qingwa2009/MyBLEGamepad/pcb/01.jpg

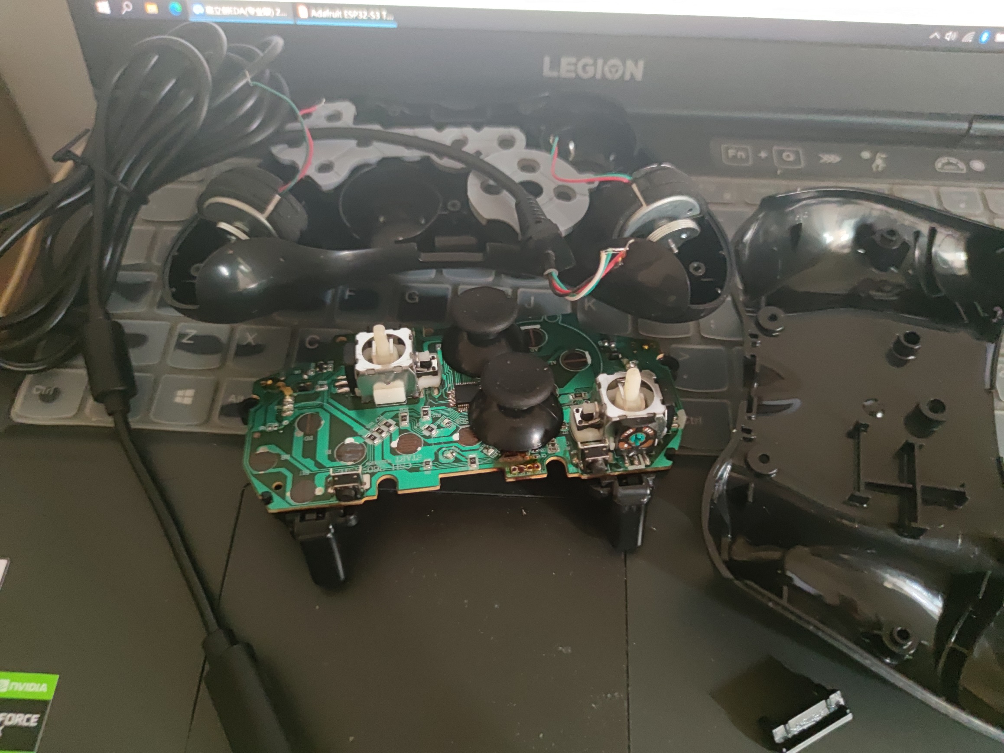
pcb/01.jpg
