qingwa2009/MyBLEGamepad/pcb/02.jpg

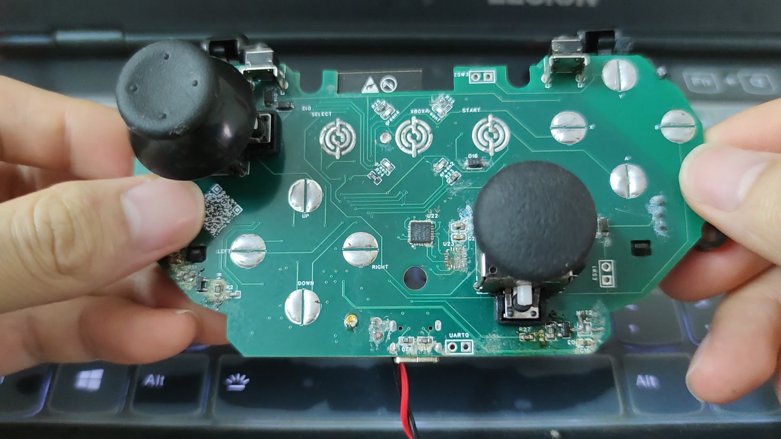
pcb/02.jpg
