qingwa2009/MyBLEGamepad/pcb/03.jpg

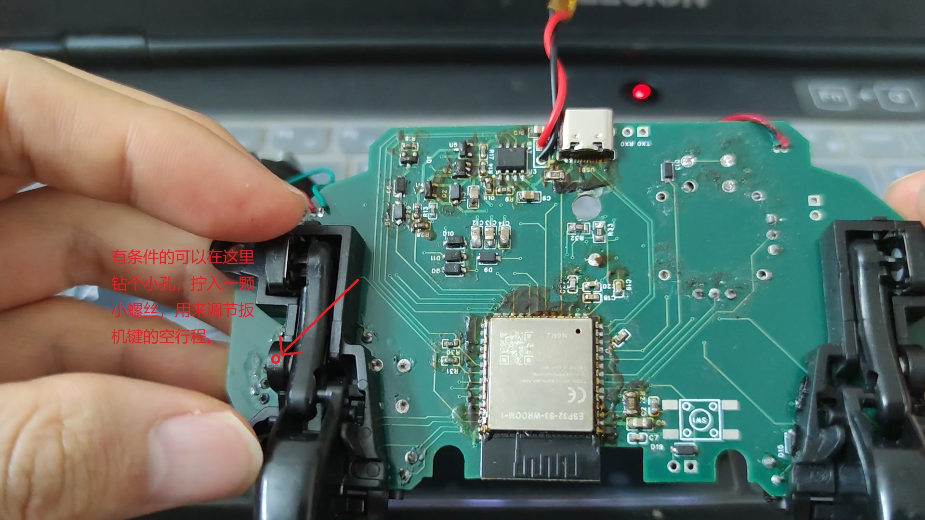
pcb/03.jpg
