qingwa2009/MyBLEGamepad/pcb/04.jpg

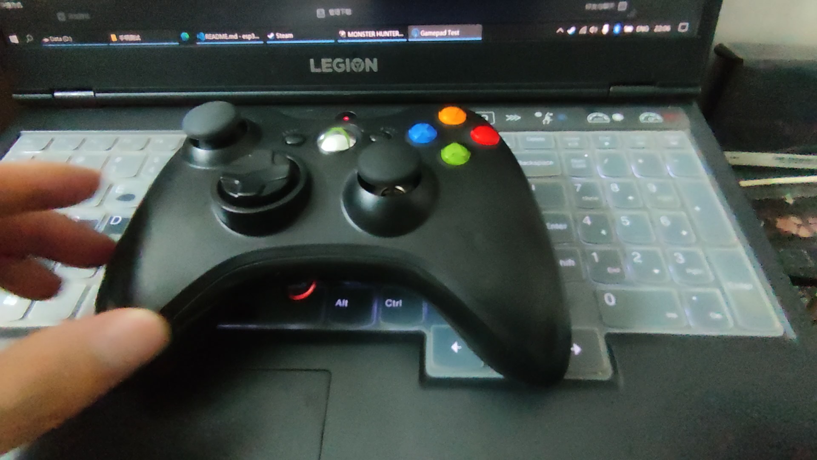
pcb/04.jpg
