qingwa2009/MyBLEGamepad/pcb/05.jpg

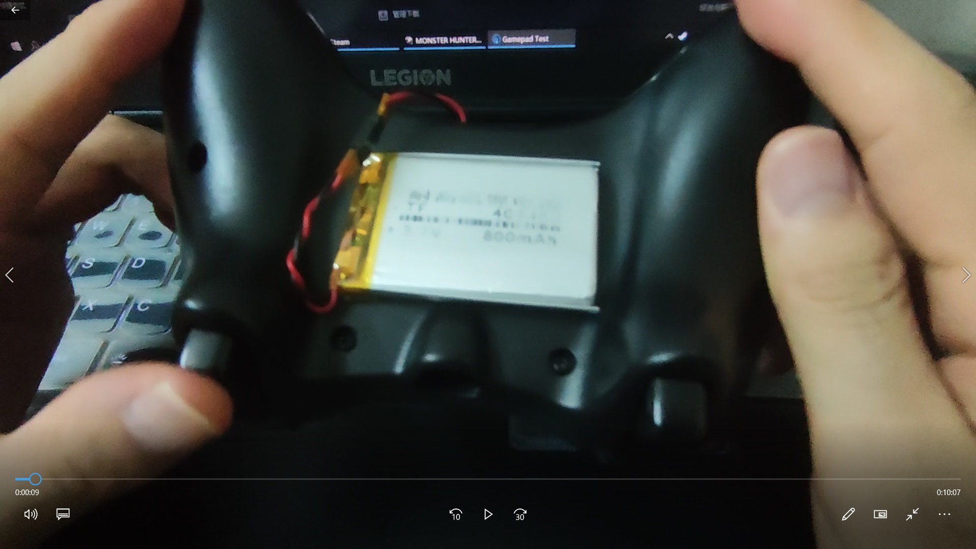
pcb/05.jpg
